safrimus/quiet-cool-rf-remote/quietcool-fan-example.yaml

esphome:
  name: quietcool-junk
  friendly_name: QuietCoolFan-junk

esp32:
  board: esp32dev
  framework:
    type: arduino

# Enable logging
logger:

# Enable Home Assistant API
api:
  encryption:
    key: !secret api_enctryption_key

ota:
  - platform: esphome
    password: !secret ota_password

wifi:
  ssid: !secret wifi_ssid
  password: !secret wifi_password

  # Enable fallback hotspot (captive portal) in case wifi connection fails
  ap:
    ssid: "Quietcool Fallback Hotspot"
    password: "iifozSf0C018"

captive_portal:

# SPI bus configuration (adjust pins as needed for your hardware)
spi:
  clk_pin: 18
  mosi_pin: 23
  miso_pin: 19

external_components:
  - source:
      type: local
      path: components
    components: [quiet_cool]

fan:
  - platform: quiet_cool
    name: QuietCool fan
    cs_pin: 15
    gdo0_pin: 13
    gdo2_pin: 12
    remote_id: [0x2D, 0xD4, 0x06, 0xCB, 0x00, 0xF7, 0xF2]
